promesoft/KicadJE_Util/PWM_Test_OpAmp_Timeshift.asc

C1: cap; 100n
C4: cap; 100n
C5: cap; 1µ
C6: cap; 100n
D1: diode; 1N914
D2: diode
D4: diode; 1N4148
R1: res; 100k
R2: res; 100k
R3: res; 1k
R4: res; 100k
R5: res; 100k
R6: res; 100k
R7: res; 20k
R8: res; 100k
R9: res; 1k
R10: res; 1k
R11: res; 20k
R12: res; 100k
U1: UniversalOpamp2
U2: UniversalOpamp2
U3: UniversalOpamp2
U4: UniversalOpamp2
V1: voltage; PULSE(0 5 10n 10n 10n 20m 50m 200)
V4: voltage; 5
Named nets: 0, opamp, gen, in4, in3, in1, in2, opamp2
.tran 0 5 0
